dragos473/INKTIME-Ciobanu_Dragos_333CD/Images/PCBTop.PNG

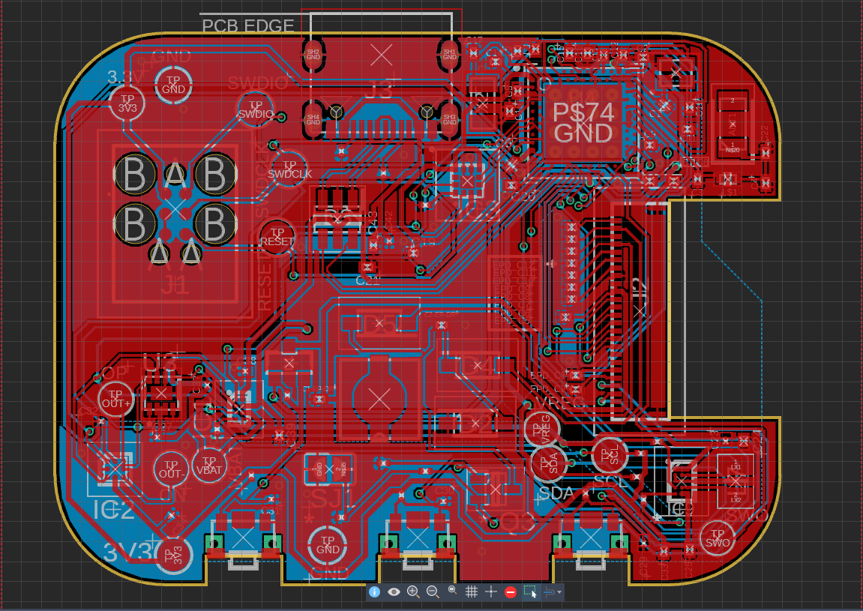
Images/PCBTop.PNG
