dragos473/INKTIME-Ciobanu_Dragos_333CD/Images/Silkscreen.PNG

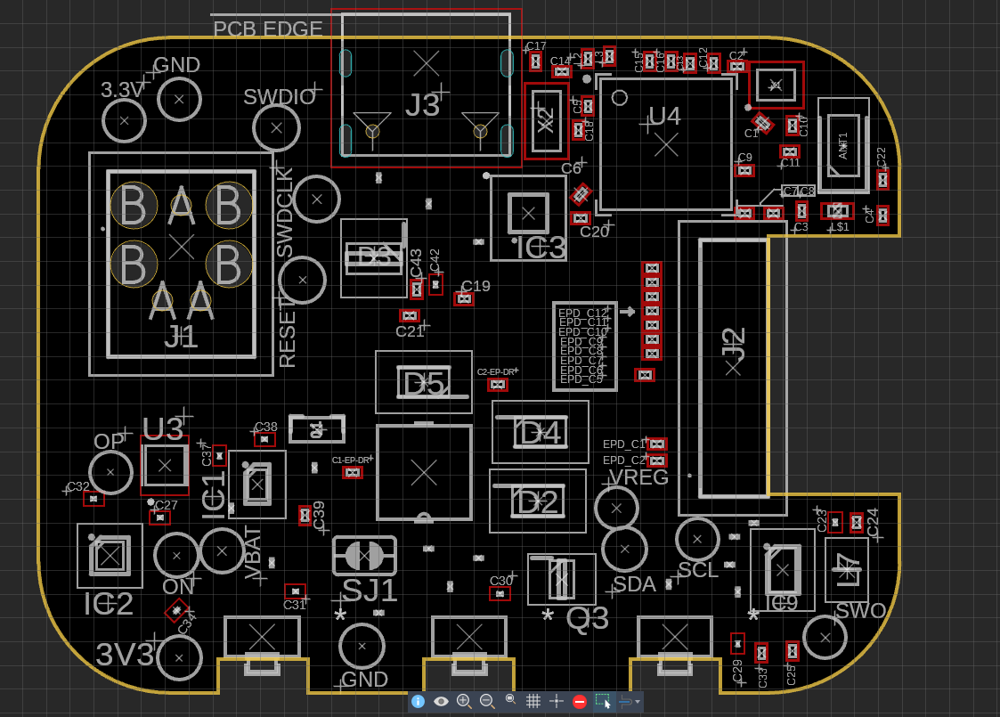
Images/Silkscreen.PNG
